s-grundner/MoodBearsKB/ecad/MoodBearsKB/TOTEM3D/D_SOD-123.step

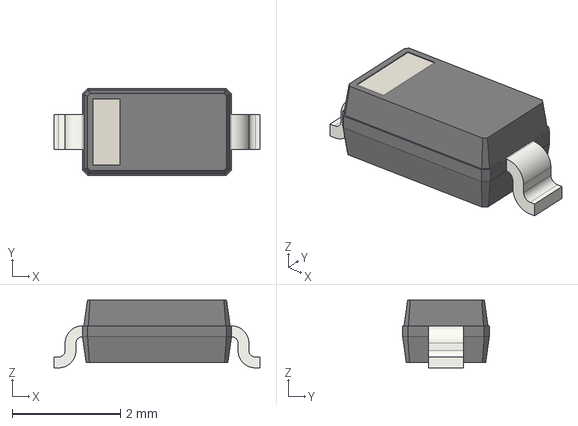
[picture p17: CAD file, 2025-06-15]
ecad/MoodBearsKB/TOTEM3D/D_SOD-123.step
3.80 x 1.60 x 1.25 mm
