s-grundner/MoodBearsKB/mcad/BLE/Redux/left/totem_ble_left_bottom_hotswap.stl

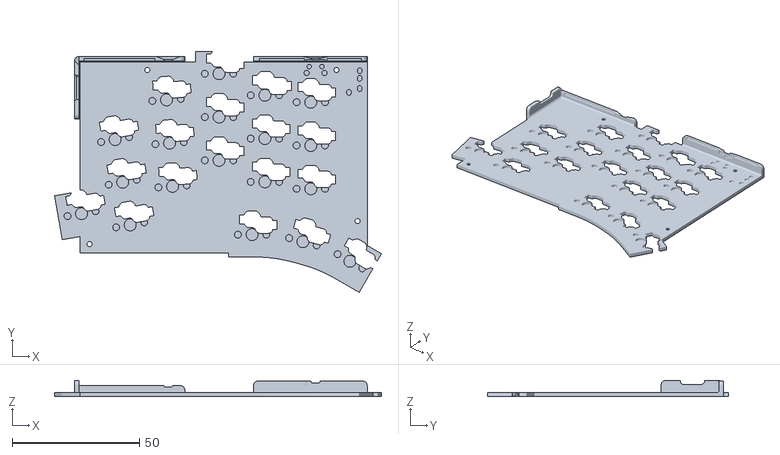
[picture p18: CAD file, 2026-06-28]
mcad/BLE/Redux/left/totem_ble_left_bottom_hotswap.stl
128.3 x 94.5 x 6.40
