s-grundner/MoodBearsKB/mcad/BLE/Redux/right/totem_ble_right_top_no_logo_m2_inserts.stl

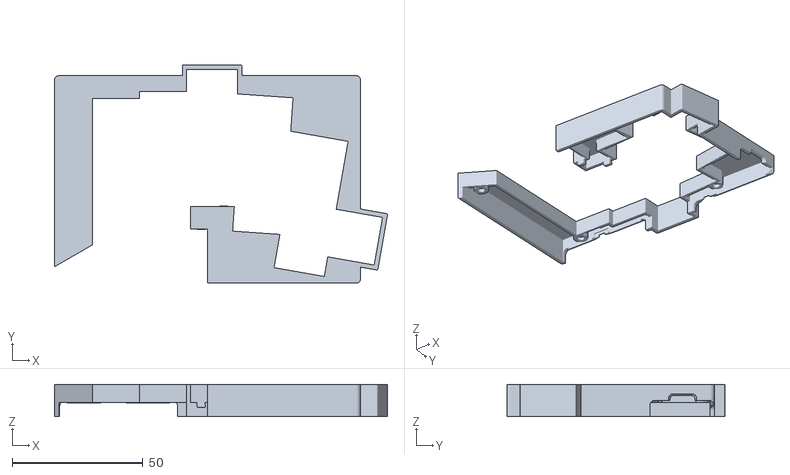
[picture p19: CAD file, 2026-06-28]
mcad/BLE/Redux/right/totem_ble_right_top_no_logo_m2_inserts.stl
127.4 x 83.5 x 12.4
