s-grundner/MoodBearsKB/mcad/KLP-Lame-Keycaps/Printing/[Choc] Normal.3mf

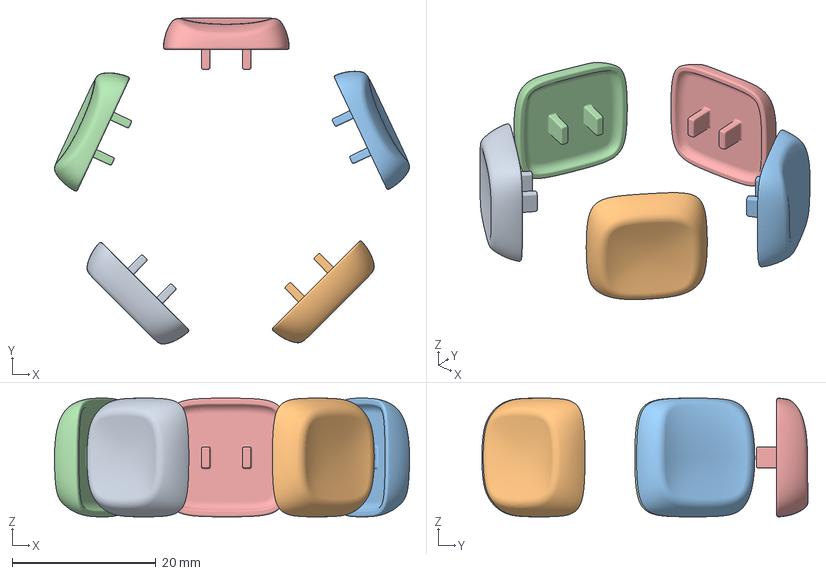
[picture p20: CAD file, 2026-06-28]
mcad/KLP-Lame-Keycaps/Printing/[Choc] Normal.3mf
49.3 x 45.3 x 16.5 mm
[Choc] Normal - FDM.stl x 2
[Choc] Thumb - FDM.stl x 3
