s-grundner/MoodBearsKB/mcad/KLP-Lame-Keycaps/STEP/Choc Stem + Choc Size/Choc_Stem_Choc_Size_Normal_Tilted.step

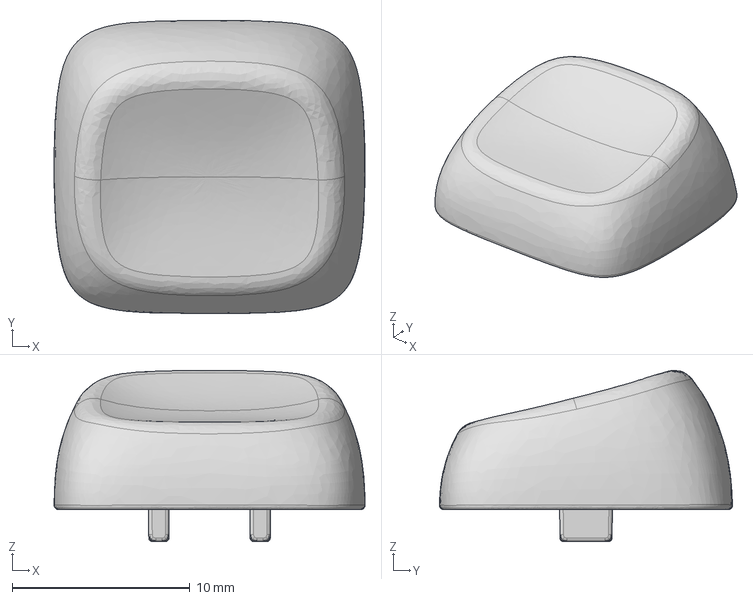
[picture p22: CAD file, 2026-06-28]
mcad/KLP-Lame-Keycaps/STEP/Choc Stem + Choc Size/Choc_Stem_Choc_Size_Normal_Tilted.step
17.5 x 16.5 x 9.63 mm
