s-grundner/MoodBearsKB/mcad/KLP-Lame-Keycaps/STEP/Choc Stem + MX Size/Choc_Stem_MX_Size_Thumb.step

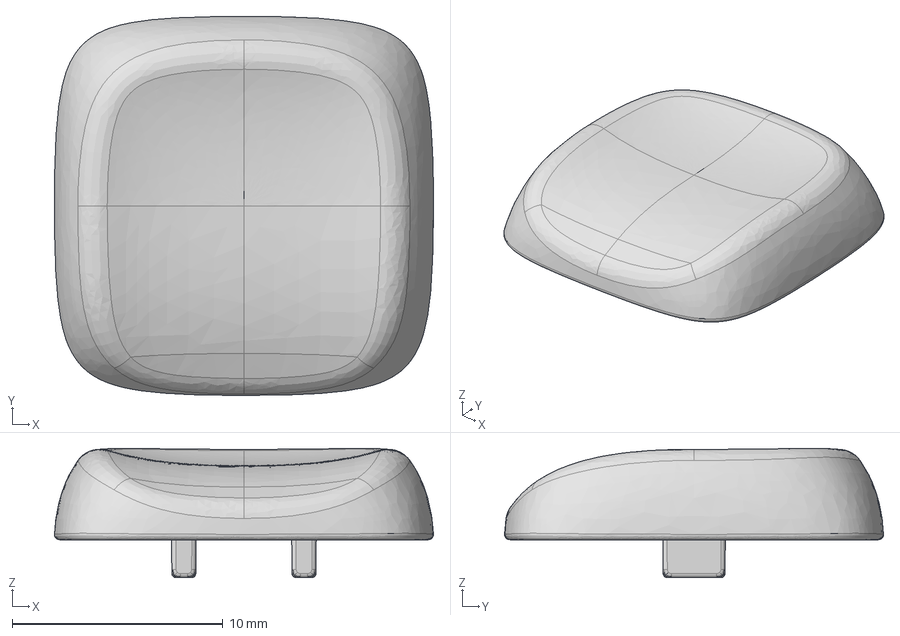
[picture p23: CAD file, 2026-06-28]
mcad/KLP-Lame-Keycaps/STEP/Choc Stem + MX Size/Choc_Stem_MX_Size_Thumb.step
18.0 x 18.0 x 6.14 mm
