s-grundner/MoodBearsKB/mcad/KLP-Lame-Keycaps/STEP/MX Stem + Choc Size/MX_Stem_Choc_Size_Saddle_Homing.step

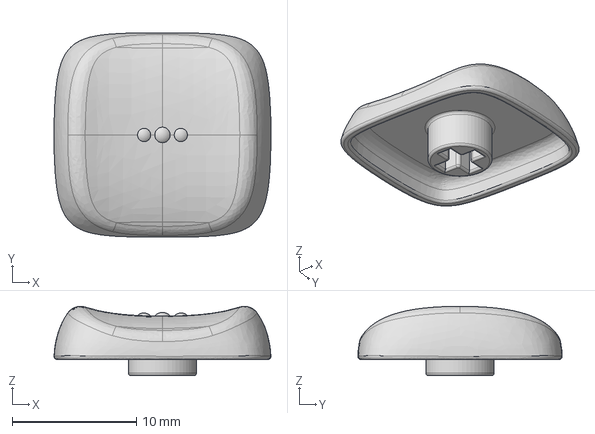
[picture p24: CAD file, 2026-06-28]
mcad/KLP-Lame-Keycaps/STEP/MX Stem + Choc Size/MX_Stem_Choc_Size_Saddle_Homing.step
17.5 x 16.5 x 5.58 mm
