s-grundner/MoodBearsKB/mcad/KLP-Lame-Keycaps/STEP/MX Stem + MX Size/MX_Stem_MX_Size_Saddle.step

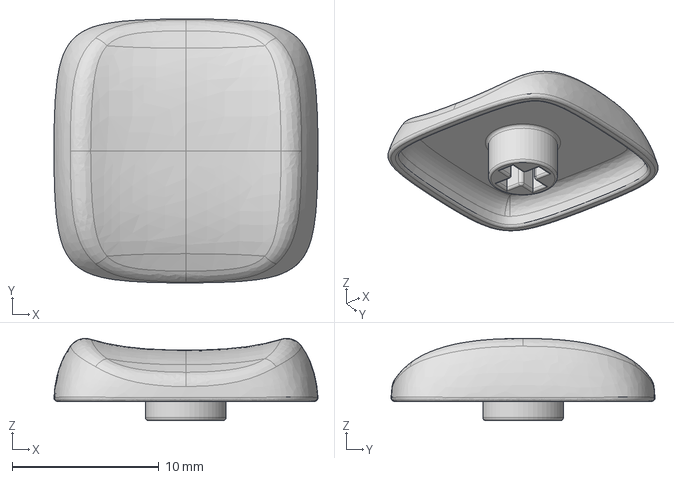
[picture p25: CAD file, 2026-06-28]
mcad/KLP-Lame-Keycaps/STEP/MX Stem + MX Size/MX_Stem_MX_Size_Saddle.step
18.0 x 18.0 x 5.59 mm
