s-grundner/MoodBearsKB/mcad/MoteCaps/mote-flat.step

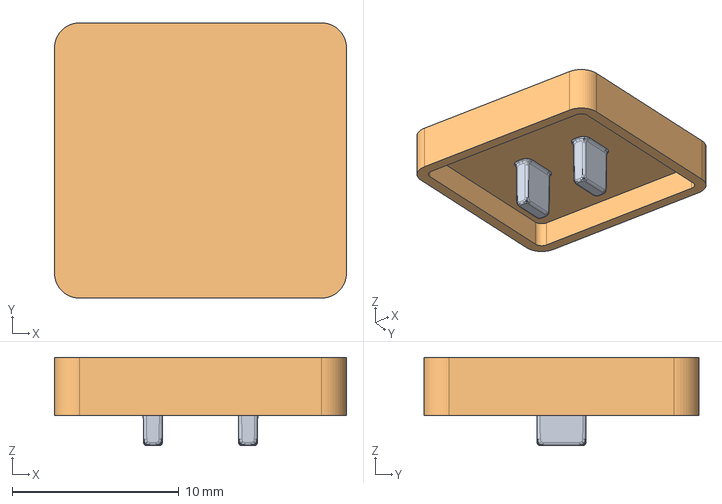
[picture p27: CAD file, 2026-06-28]
mcad/MoteCaps/mote-flat.step
17.5 x 16.5 x 5.30 mm
