s-grundner/MoodBearsKB/mcad/slices/[Choc] Normal Tilted.3mf

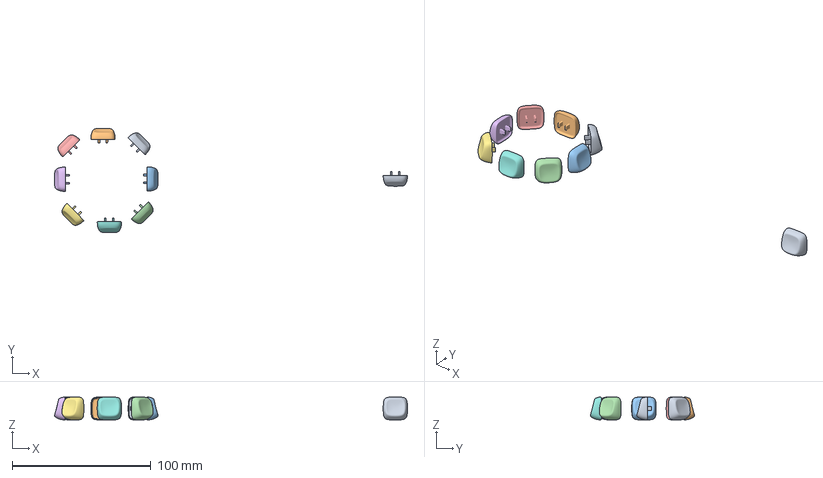
[picture p28: CAD file, 2026-06-30]
mcad/slices/[Choc] Normal Tilted.3mf
254.2 x 75.1 x 16.5 mm
[Choc] Normal Tilted - FDM.stl x 9
