s-grundner/MoodBearsKB/mcad/slices/stl/SwitchPlateR.stl

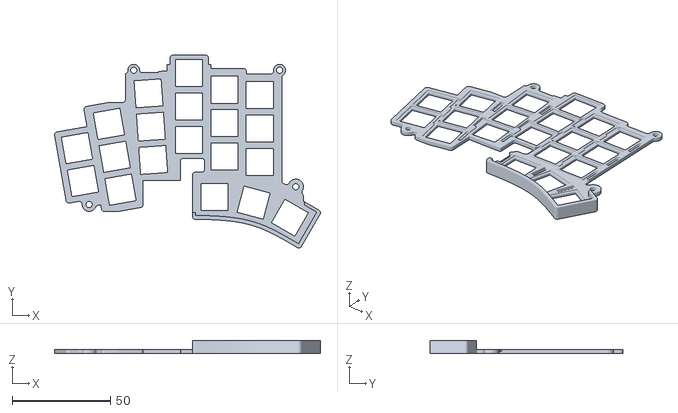
[picture p29: CAD file, 2026-06-30]
mcad/slices/stl/SwitchPlateR.stl
135.4 x 98.3 x 6.45
