s-grundner/MoodBearsKB/mcad/KLP-Lame-Keycaps/STEP/Choc Stem + Choc Size/90 deg Rotated/Choc_Stem_Choc_Size_Normal_Tilted_90deg.step

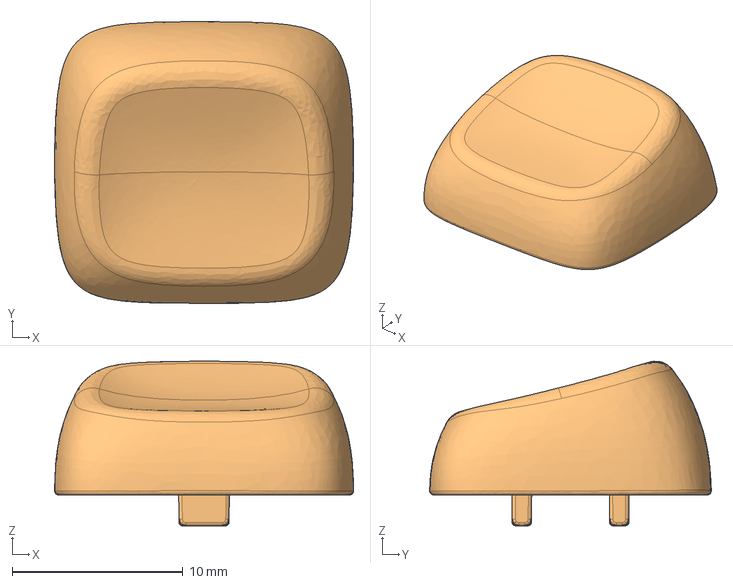
[picture p31: CAD file, 2026-06-28]
mcad/KLP-Lame-Keycaps/STEP/Choc Stem + Choc Size/90 deg Rotated/Choc_Stem_Choc_Size_Normal_Tilted_90deg.step
17.5 x 16.5 x 9.63 mm
