s-grundner/MoodBearsKB/mcad/KLP-Lame-Keycaps/STEP/Choc Stem + Choc Size/Choc_Stem_Choc_Size_Thumb.step

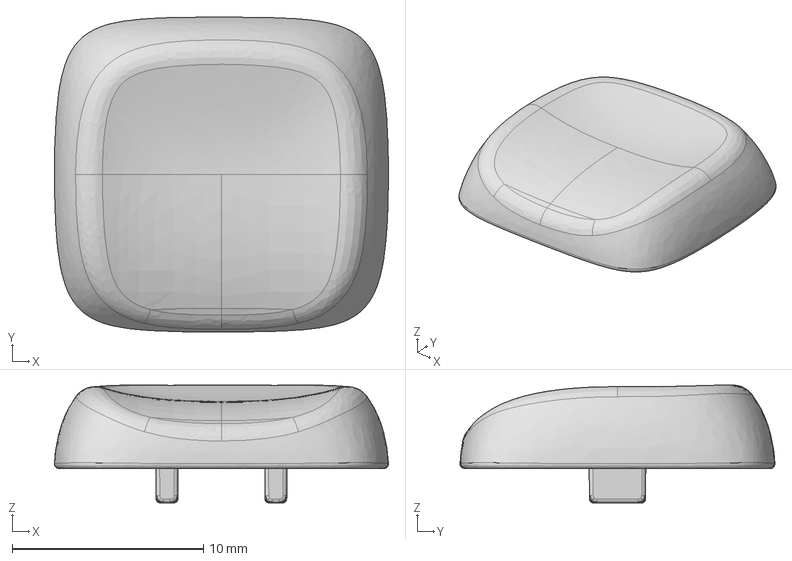
[picture p32: CAD file, 2026-06-28]
mcad/KLP-Lame-Keycaps/STEP/Choc Stem + Choc Size/Choc_Stem_Choc_Size_Thumb.step
17.5 x 16.5 x 6.17 mm
