s-grundner/MoodBearsKB/mcad/KLP-Lame-Keycaps/STEP/Choc Stem + MX Size/Choc_Stem_MX_Size_Normal_Tilted.step

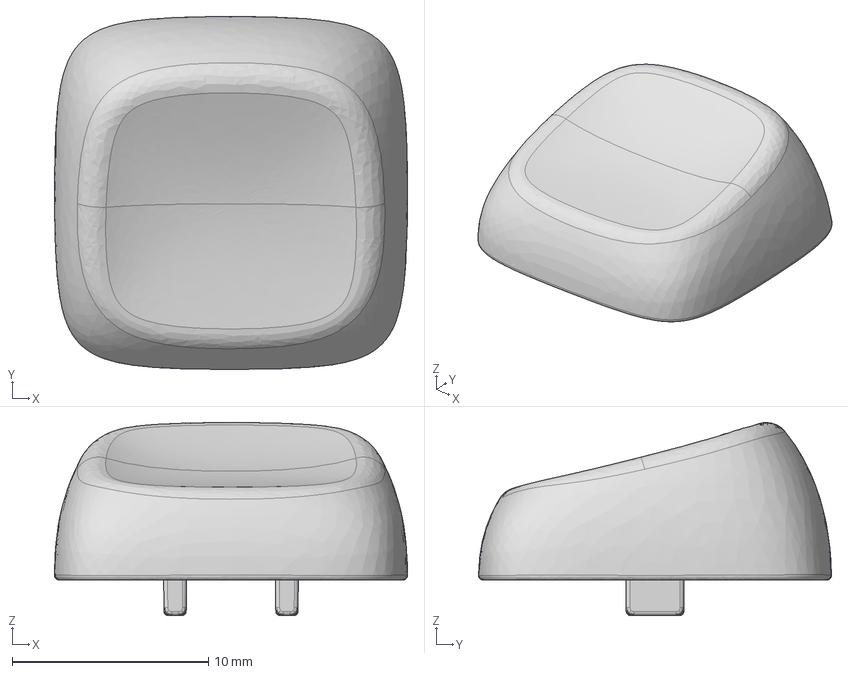
[picture p33: CAD file, 2026-06-28]
mcad/KLP-Lame-Keycaps/STEP/Choc Stem + MX Size/Choc_Stem_MX_Size_Normal_Tilted.step
18.0 x 18.0 x 9.84 mm
