s-grundner/MoodBearsKB/mcad/KLP-Lame-Keycaps/STEP/MX Stem + Choc Size/MX_Stem_Choc_Size_Normal_Tilted.step

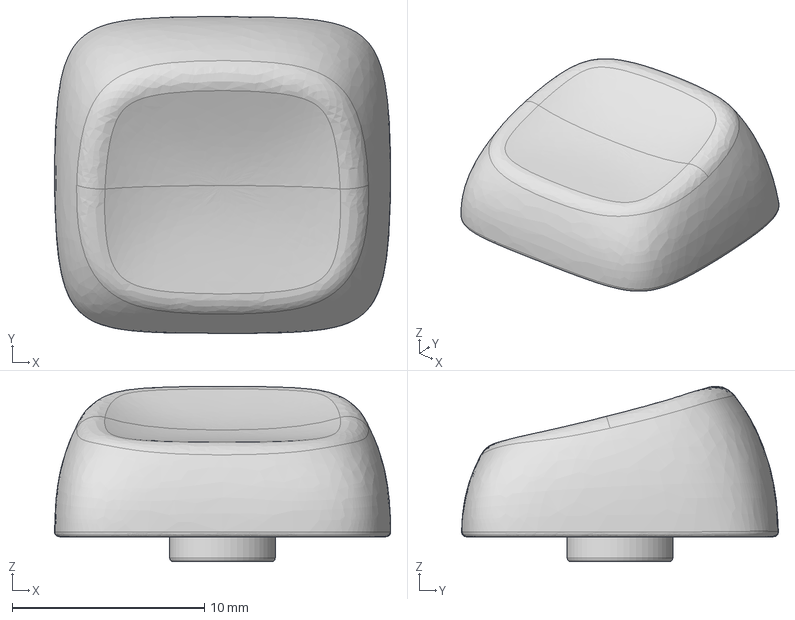
[picture p34: CAD file, 2026-06-28]
mcad/KLP-Lame-Keycaps/STEP/MX Stem + Choc Size/MX_Stem_Choc_Size_Normal_Tilted.step
17.5 x 16.5 x 9.13 mm
