s-grundner/MoodBearsKB/mcad/KLP-Lame-Keycaps/STL/Choc Stem + Choc Size/Smino Edits/[Choc] Thumb - FDM.stl

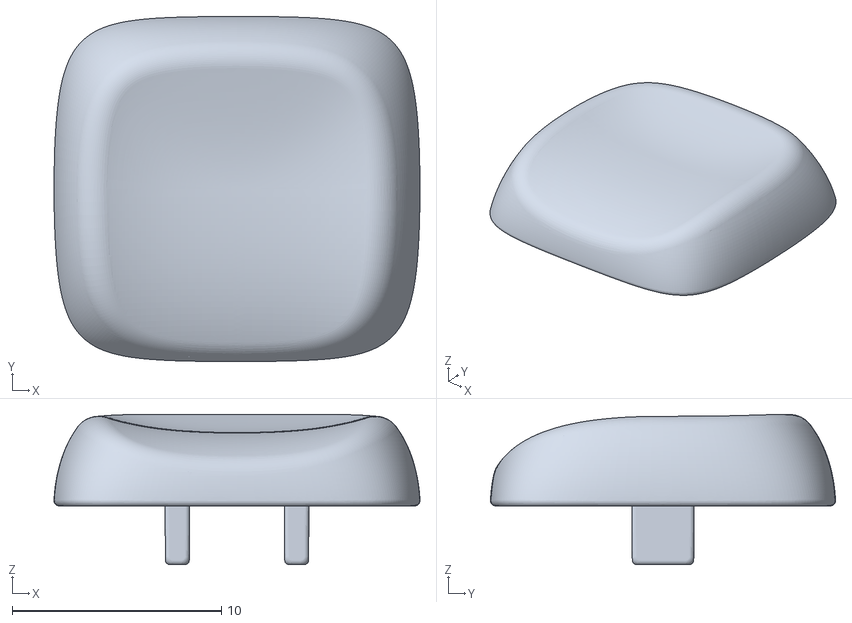
[picture p36: CAD file, 2026-06-28]
mcad/KLP-Lame-Keycaps/STL/Choc Stem + Choc Size/Smino Edits/[Choc] Thumb - FDM.stl
17.5 x 16.5 x 7.17
