s-grundner/MoodBearsKB/mcad/MoteCaps/mote-angled-rotated.step

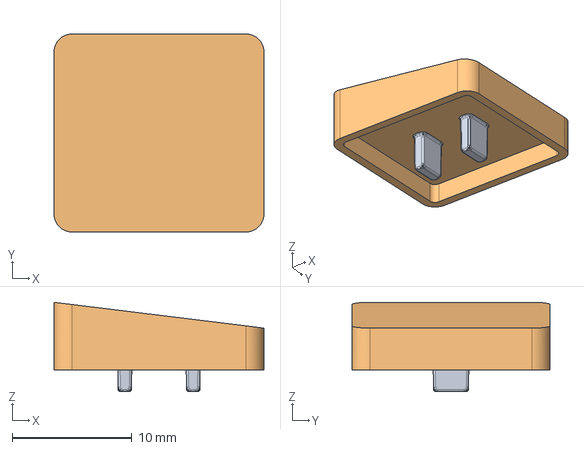
[picture p37: CAD file, 2026-06-28]
mcad/MoteCaps/mote-angled-rotated.step
17.5 x 16.5 x 7.45 mm
