s-grundner/MoodBearsKB/mcad/slices/[Choc] Normal.3mf

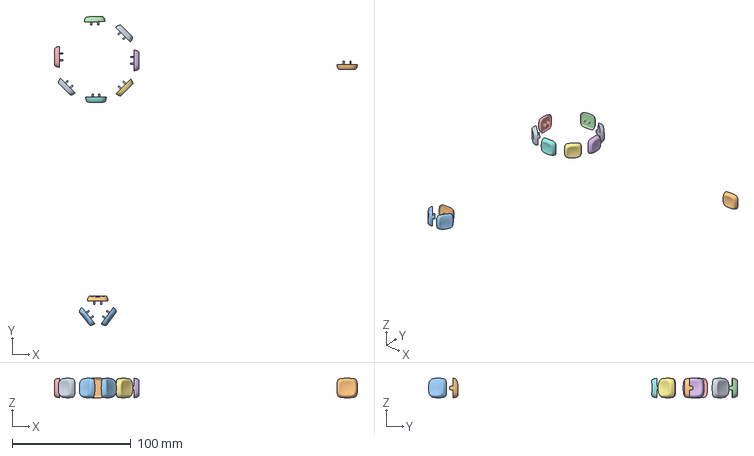
[picture p38: CAD file, 2026-06-30]
mcad/slices/[Choc] Normal.3mf
255.3 x 260.3 x 16.5 mm
[Choc] Normal - FDM.stl x 8
[Choc] Thumb - FDM.stl x 3
