s-grundner/MoodBearsKB/mcad/slices/stl/BaseL.stl

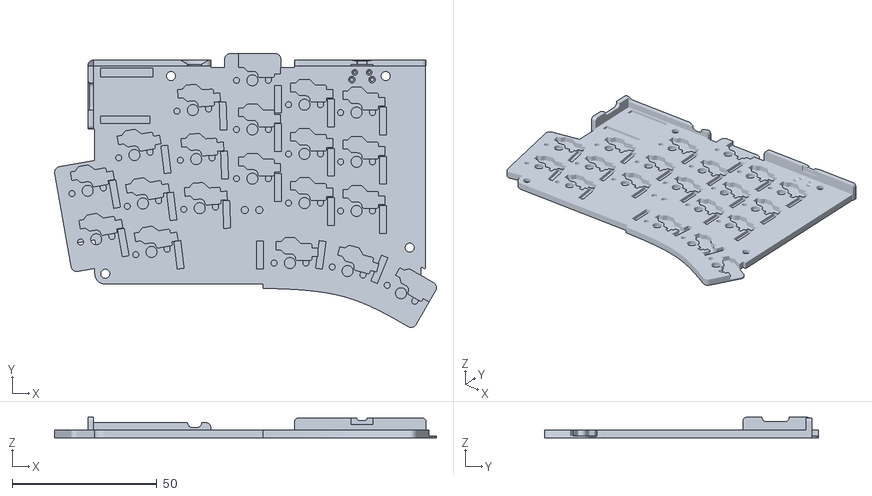
[picture p39: CAD file, 2026-06-30]
mcad/slices/stl/BaseL.stl
132.0 x 94.7 x 7.20
