s-grundner/MoodBearsKB/ecad/MoodBearsKB/TOTEM3D/PJ320A.STEP

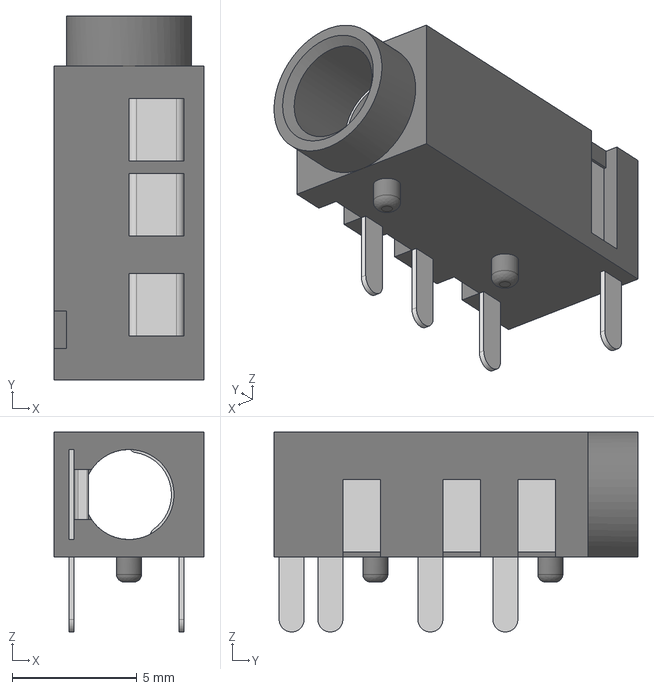
[picture p40: CAD file, 2025-06-15]
ecad/MoodBearsKB/TOTEM3D/PJ320A.STEP
6.00 x 14.6 x 8.00 mm
