s-grundner/MoodBearsKB/mcad/KLP-Lame-Keycaps/STEP/Choc Stem + MX Size/Choc_Stem_MX_Size_Normal_Homing.step

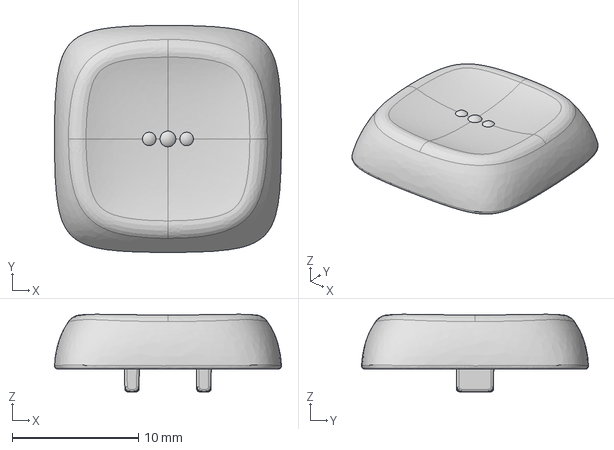
[picture p42: CAD file, 2026-06-28]
mcad/KLP-Lame-Keycaps/STEP/Choc Stem + MX Size/Choc_Stem_MX_Size_Normal_Homing.step
18.0 x 18.0 x 6.14 mm
