s-grundner/MoodBearsKB/mcad/KLP-Lame-Keycaps/STEP/MX Stem + MX Size/MX_Stem_MX_Size_Saddle_Tilted.step

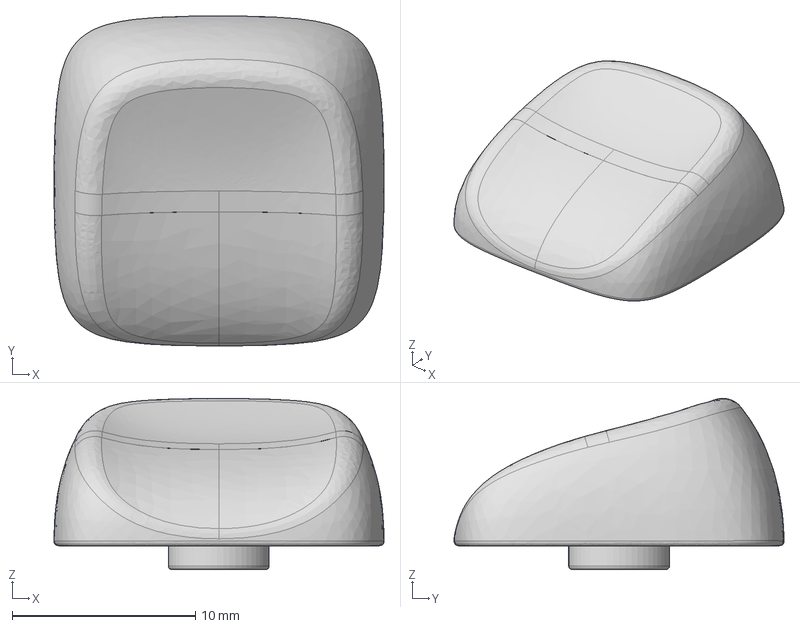
[picture p43: CAD file, 2026-06-28]
mcad/KLP-Lame-Keycaps/STEP/MX Stem + MX Size/MX_Stem_MX_Size_Saddle_Tilted.step
18.0 x 18.0 x 9.34 mm
