s-grundner/MoodBearsKB/mcad/slices/testCap.3mf

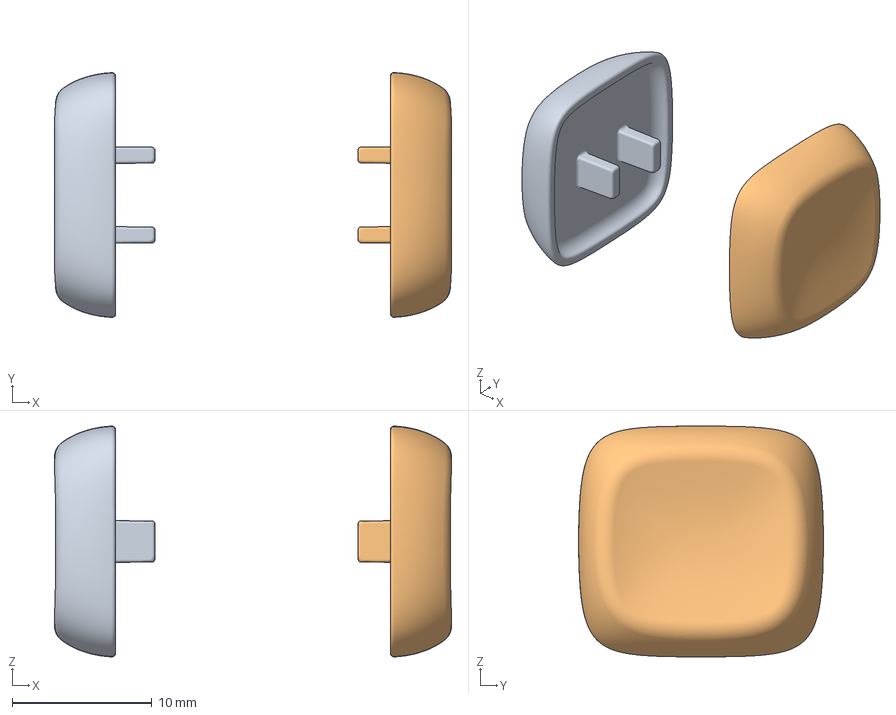
[picture p44: CAD file, 2026-06-28]
mcad/slices/testCap.3mf
28.4 x 17.5 x 16.5 mm
[Choc] Normal - FDM.stl
[Choc] Normal - FDM Light.stl
