s-grundner/MoodBearsKB/ecad/MoodBearsKB/TOTEM3D/MSK12C02.STEP

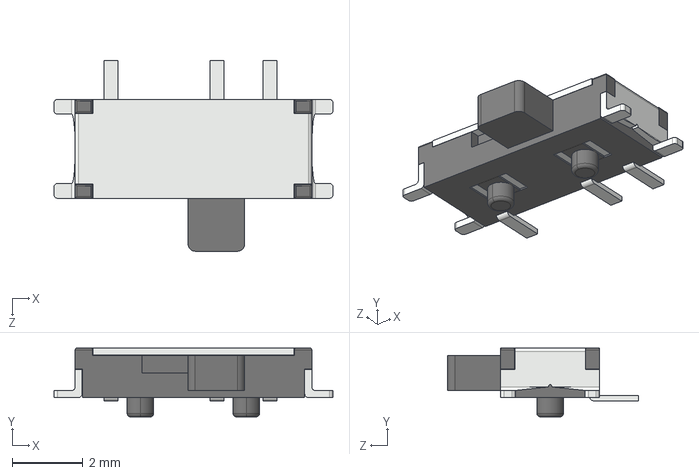
[picture p45: CAD file, 2025-06-15]
ecad/MoodBearsKB/TOTEM3D/MSK12C02.STEP
7.90 x 1.95 x 5.39 mm
