s-grundner/MoodBearsKB/mcad/KLP-Lame-Keycaps/STEP/MX Stem + Choc Size/MX_Stem_Choc_Size_Thumb.step

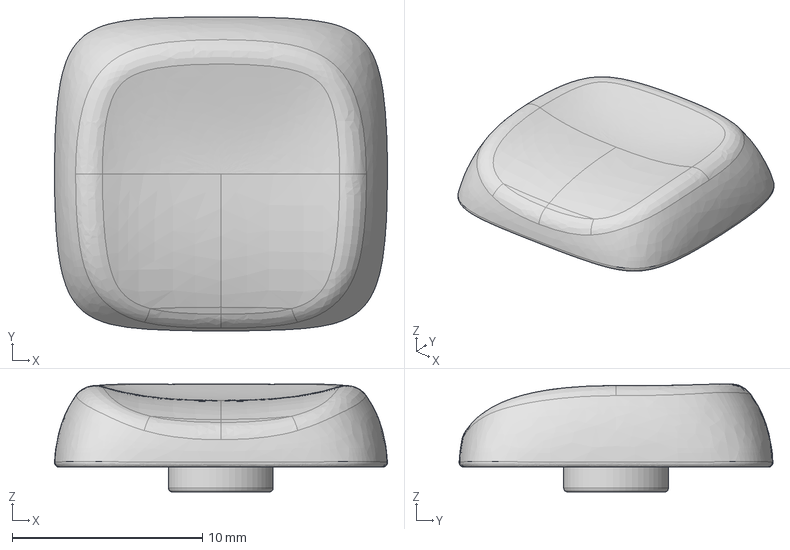
[picture p46: CAD file, 2026-06-28]
mcad/KLP-Lame-Keycaps/STEP/MX Stem + Choc Size/MX_Stem_Choc_Size_Thumb.step
17.5 x 16.5 x 5.67 mm
