s-grundner/MoodBearsKB/mcad/KLP-Lame-Keycaps/STEP/MX Stem + MX Size/MX_Stem_MX_Size_Normal_Homing.step

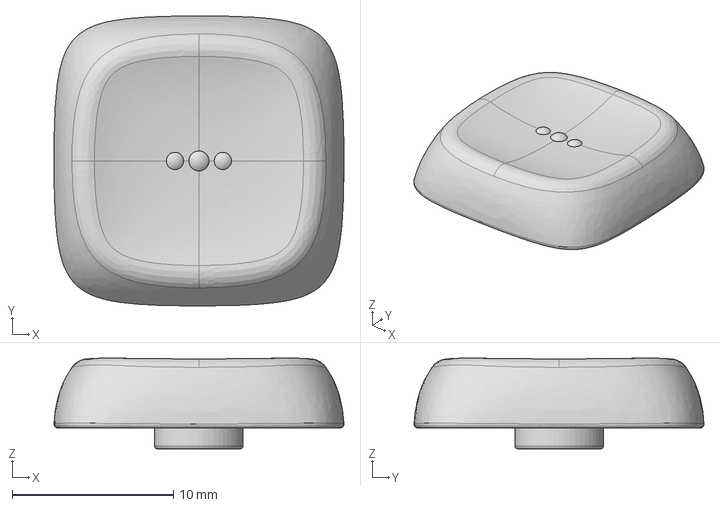
[picture p47: CAD file, 2026-06-28]
mcad/KLP-Lame-Keycaps/STEP/MX Stem + MX Size/MX_Stem_MX_Size_Normal_Homing.step
18.0 x 18.0 x 5.64 mm
