s-grundner/MoodBearsKB/ecad/MoodBearsKB/TOTEM3D/SW_SKHLLC.step

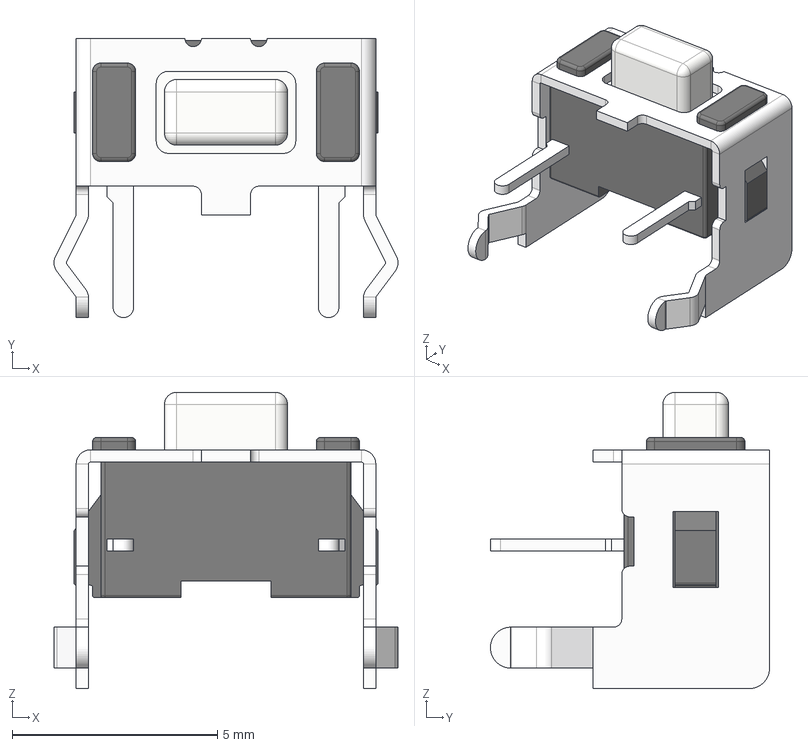
[picture p48: CAD file, 2025-06-15]
ecad/MoodBearsKB/TOTEM3D/SW_SKHLLC.step
8.38 x 6.80 x 7.22 mm
