s-grundner/MoodBearsKB/ecad/MoodBearsKB/TOTEM3D/Kailh_socket_PG1350_optional.STEP

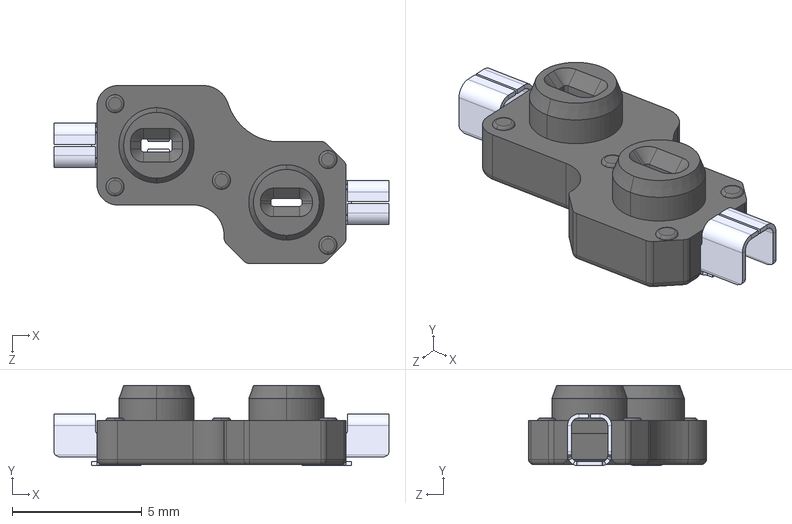
[picture p50: CAD file, 2025-06-15]
ecad/MoodBearsKB/TOTEM3D/Kailh_socket_PG1350_optional.STEP
12.9 x 3.09 x 6.85 mm
pin x 2
socket
